TinyTapeout/breakout-pcb/images/tt03-breakout.jpg

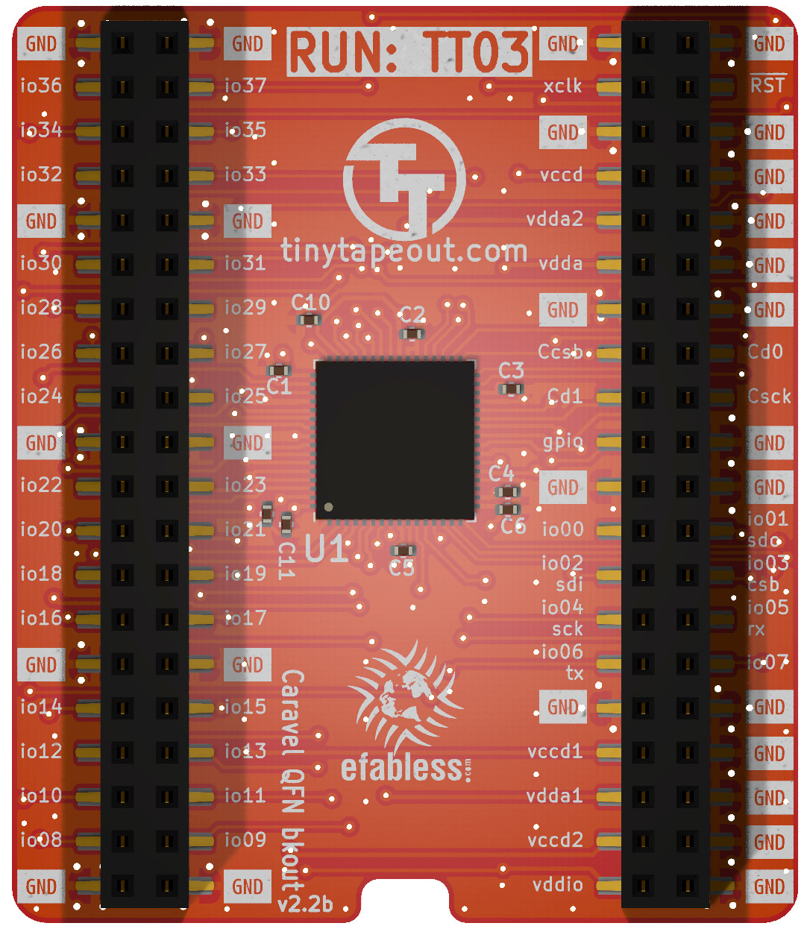
images/tt03-breakout.jpg
